ndaneil/matterdoor/imgs/connected2.jpg

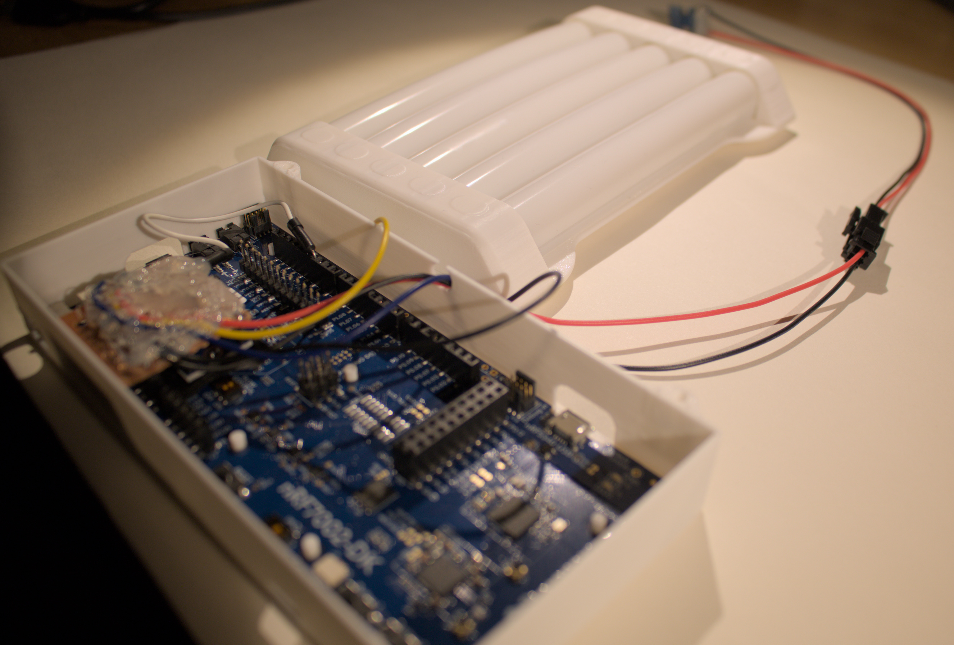
imgs/connected2.jpg
