ndaneil/matterdoor/imgs/top.jpg

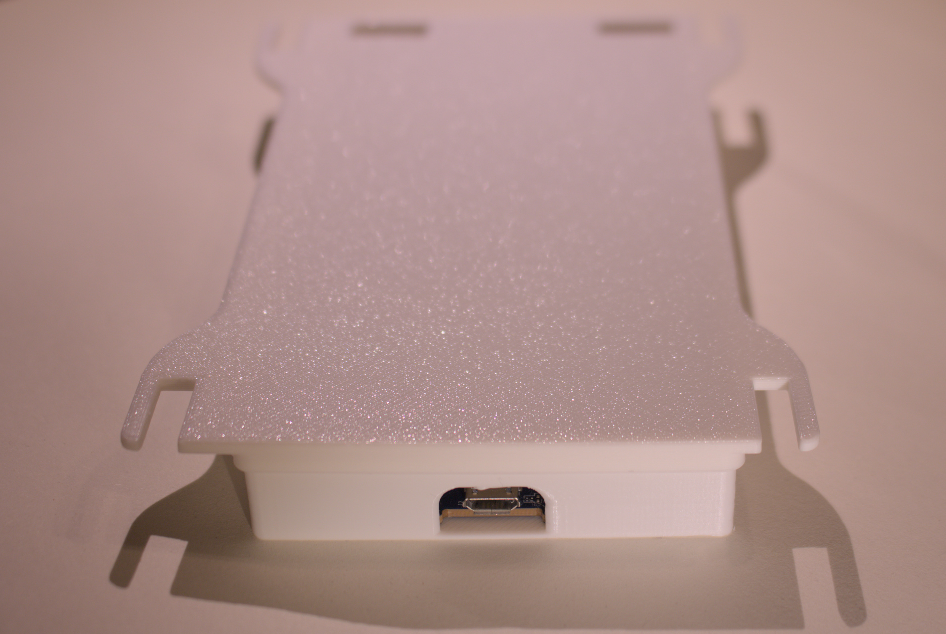
imgs/top.jpg
